jphastings/jan-poka/hardware/mapper/mapper/vars.h

#define WIFI_SSID "Porque Fi"
#define WIFI_PASS "Shanghai"
#define MQTT_HOST "192.168.86.22"
#define MQTT_PORT 1883
#define MQTT_USER "dev"
#define MQTT_PASS "devpassword"
#define MQTT_TOPIC "home/geo/target"
